SK21/TemperatureMonitor/Current Files/PCBs/TM11/TempPCB11.jpg

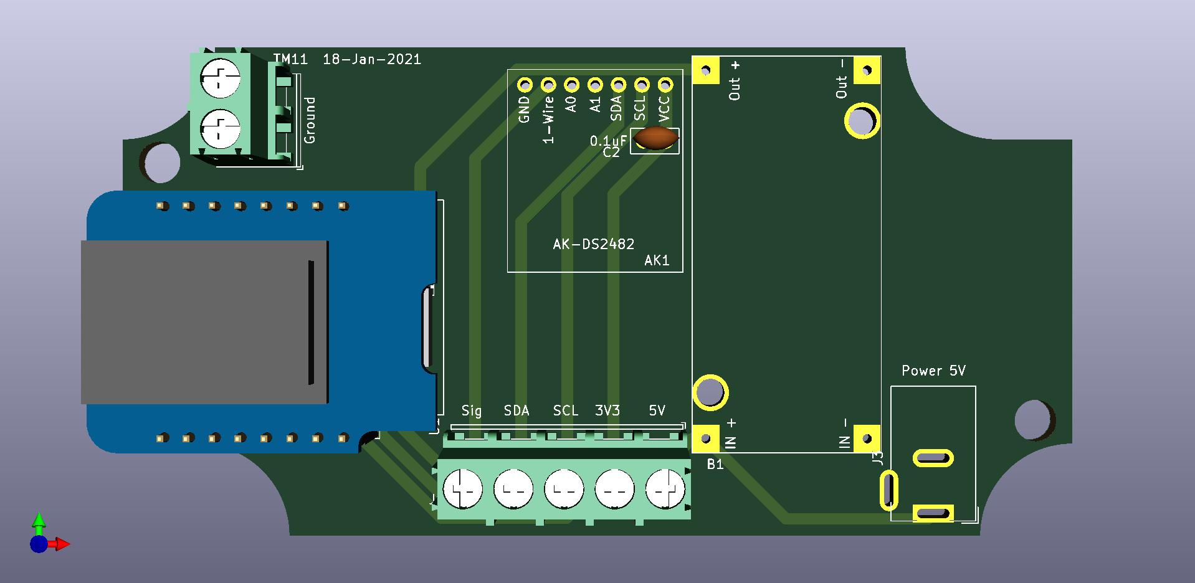
Current Files/PCBs/TM11/TempPCB11.jpg
