SK21/TemperatureMonitor/PCBs/TM13/TM13.jpg

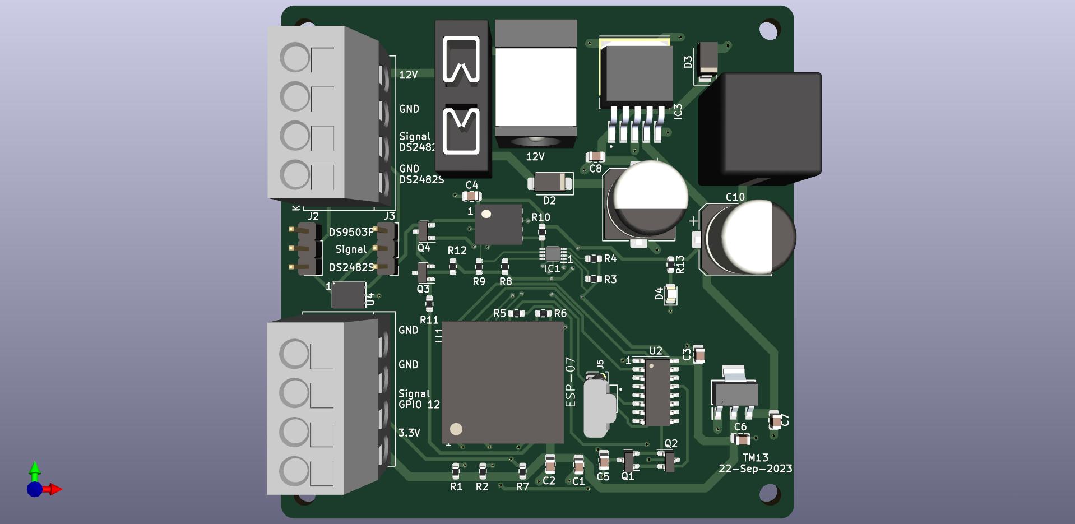
PCBs/TM13/TM13.jpg
