SK21/TemperatureMonitor/Current Files/PCBs/TM10_PCB/downImg.png

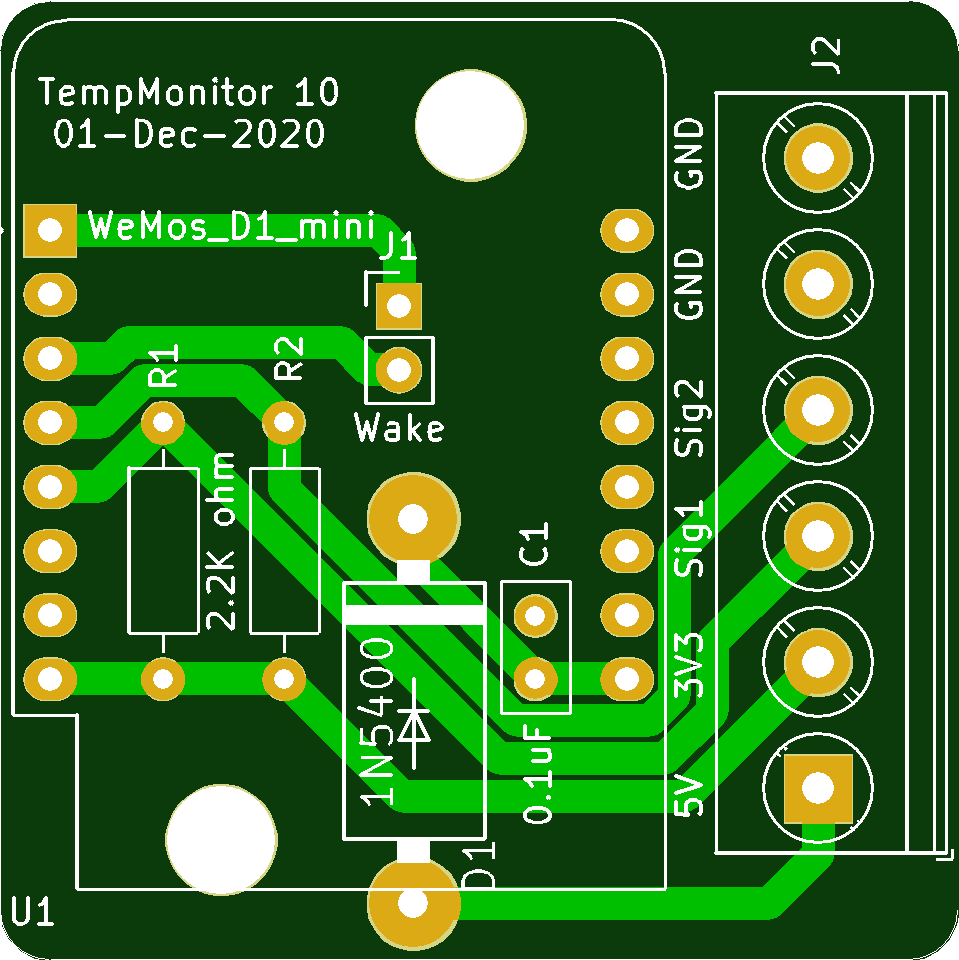
Current Files/PCBs/TM10_PCB/downImg.png
