SK21/TemperatureMonitor/Current Files/PCBs/TMS1/TMS1.jpg

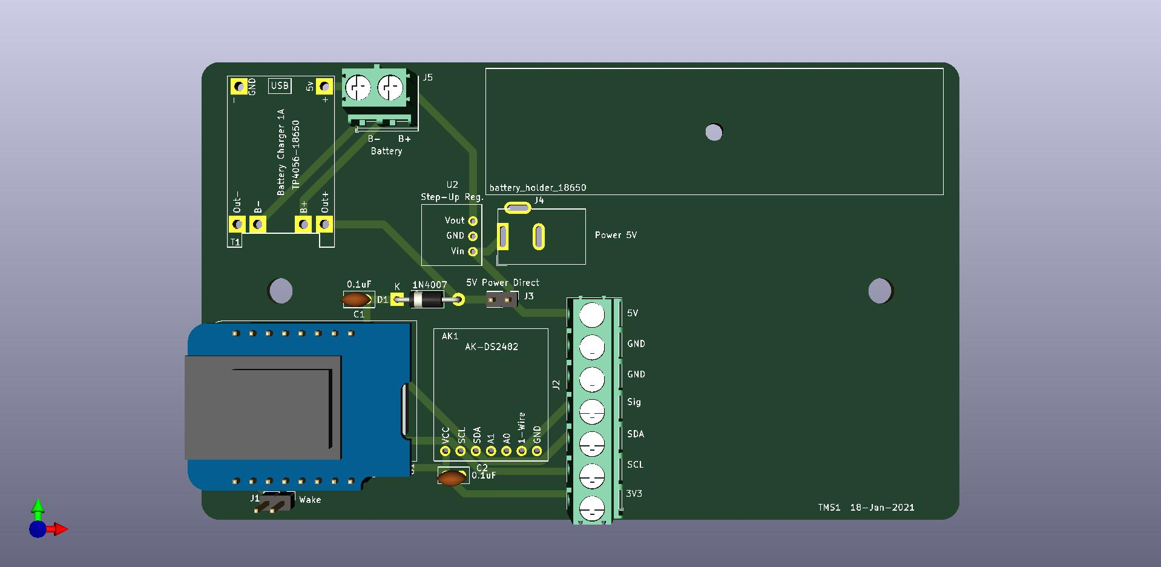
Current Files/PCBs/TMS1/TMS1.jpg
