SK21/TemperatureMonitor/PCBs/TM13/jlcpcb/production_files/quote for 5.PNG

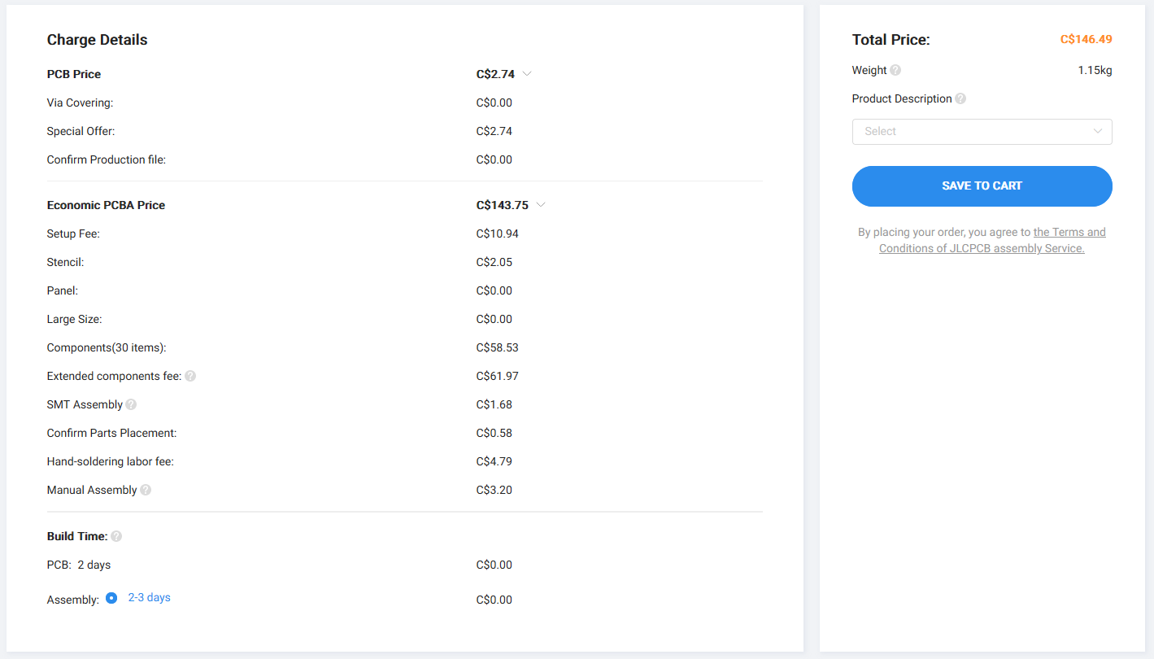
PCBs/TM13/jlcpcb/production_files/quote for 5.PNG
